thechosenone98/Ultimate-Strat/Font/Planning font.png

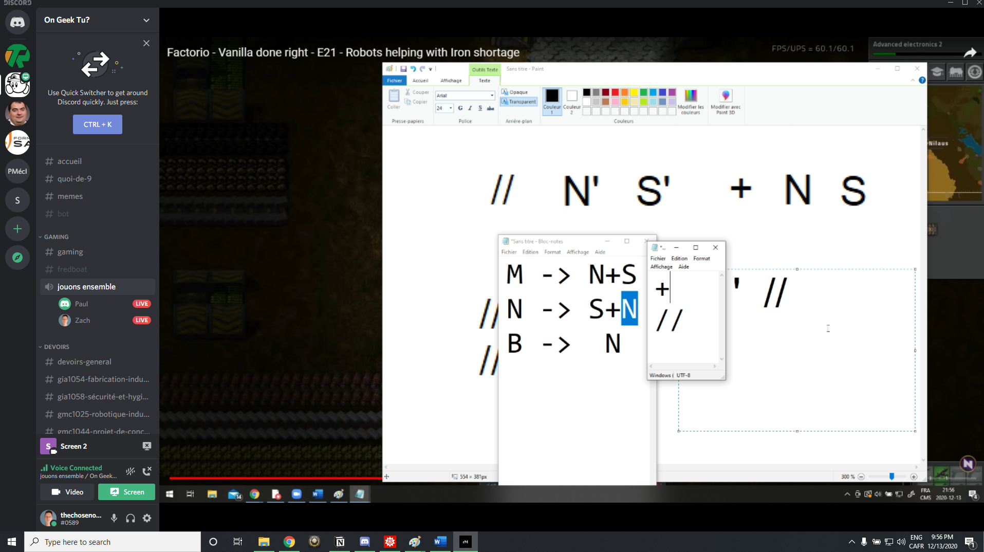
Font/Planning font.png
